ayaghini/PAKT/docs/aprs_mvp_docs/hardware/placeholder_bom.csv

Item | Preferred Part/Class | Status | Key Notes | Qty
MCU | Based on ESP32-S3 module with PSRAM | Locked | Keep UART debug/programming access | 1
RF module | SA818 VHF variant | Locked | Verify exact module supply and PTT polarity | 1
GPS | U-blox NEO-M8N class module | Locked | UART NMEA with optional PPS footprint | 1
Audio codec | SGTL5000 | Locked-Prototype | Mono path on one channel is acceptable for APRS; keep MCLK routing explicit | 1
Fuel gauge | MAX17048 | Locked | Match Adafruit Feather ESP32-S3 power telemetry baseline | 1
Charger | MCP73831/2 | Locked-PCB | Match Feather charge path; if USB-C include sink CC resistors and ESD | 1
3.3V regulator | Low-noise regulator sized for total digital load | Provisional | Separate radio rail from digital rail return | 1
Radio rail conditioning | Bulk + HF decoupling near SA818 | Required | DNP extra bulk pad recommended | 1 set
Display (optional) | SSD1306 0.96in I2C | Optional | Can be depopulated on production compact variant | 1
Antenna connector | SMA female (panel or edge based on mech) | Locked | 50-ohm controlled route from SA818 ANT | 1
PTT interface | Direct GPIO with optional transistor stage footprint | Required-Option | Keep pull resistor and DNP transistor option | 1
Audio coupling network | AC coupling caps + optional AF gain/filter network | Required | Needed for TX deviation/RX clipping tuning | 1 set
Battery | Single-cell Li-ion/LiPo | Locked | Capacity based on enclosure target | 1
Battery connector | 2-pin polarized connector | Locked | Add reverse polarity strategy | 1
Haptic driver | NPN or NMOS low-side driver | Locked | Include base/gate resistor and diode if required by motor type | 1
ESD protection | USB and exposed IO/connector protection | Required | Include at least USB and antenna-adjacent protection strategy | 1 set
Test points | Power + audio + control nets | Required | VBAT_RAW V_SYS_3V3 V_RADIO AF_TX AF_RX PTT UART nets | 1 set
