ayaghini/PAKT/docs/hardware/components/wm8960/sources.md

# WM8960 Sources (Legacy Reference)

## Status
- WM8960 is not the active baseline for this project.
- Active codec baseline is SGTL5000.

## Datasheet
- WM8960 datasheet mirror (non-authoritative)
  - https://www.alldatasheet.com/datasheet-pdf/pdf/628821/WOLFSON/WM8960.html

## Official application notes / design guidance
- WAN0129: Layout Design Considerations for ADC and DAC Devices (Cirrus Logic)
  - https://statics.cirrus.com/pubs/appNote/WAN0129.pdf

## Notes
- Keep this folder only for legacy comparison and migration history.
- Re-verify all electrical limits if WM8960 is ever reintroduced.
