ayaghini/PAKT/docs/hardware/components/max17043/sources.md

# MAX17043 Sources

## Official datasheets
- MAX17043 Product Page
  - https://www.analog.com/en/products/max17043.html
- MAX17043/MAX17044 Data Sheet (Rev. 7, PDF)
  - https://www.analog.com/media/en/technical-documentation/data-sheets/MAX17043-MAX17044.pdf

## Official application notes / design guidance
- Characterizing a Battery for Use with a Fuel Gauge
  - https://www.analog.com/en/resources/technical-articles/battery-gauge--maxim-integrated.html

## Notes
- Treat battery characterization guidance as required input to SOC accuracy targets.
